Elektroniikkakerho/Led-merkki/kicad/optiem/kuvat/IMG_20201127_135844.jpg

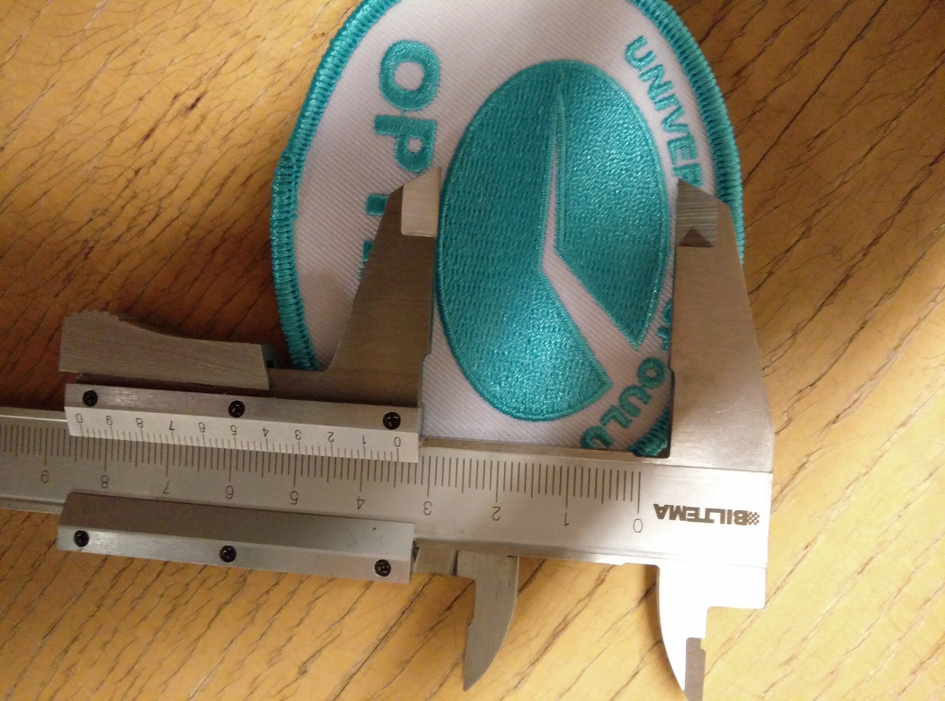
kicad/optiem/kuvat/IMG_20201127_135844.jpg
