Elektroniikkakerho/Led-merkki/kicad/optiem/kuvat/IMG_20201127_140003.jpg

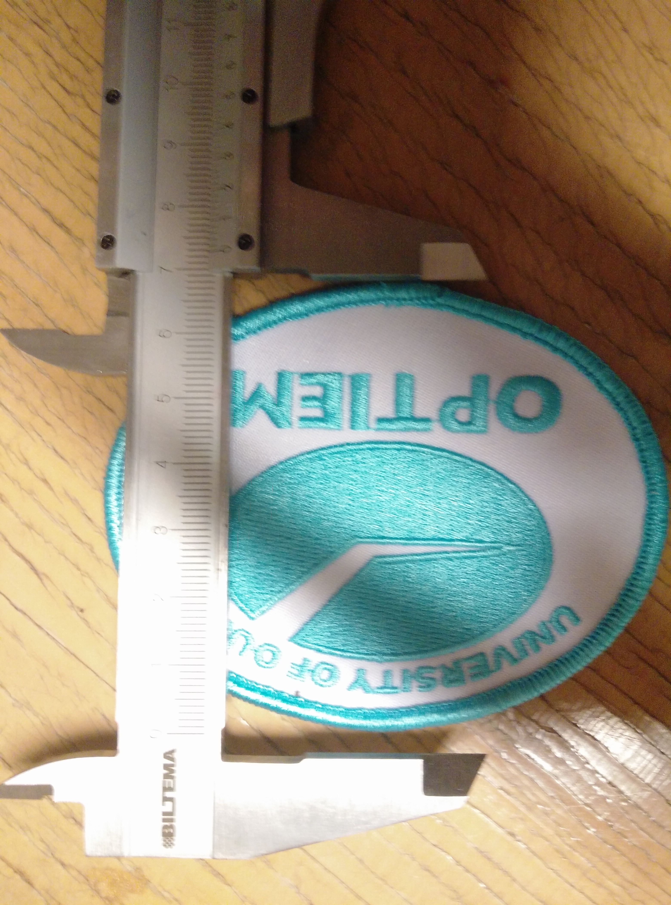
kicad/optiem/kuvat/IMG_20201127_140003.jpg
