Elektroniikkakerho/Led-merkki/kicad/optiem/kuvat/IMG_20201127_140038.jpg

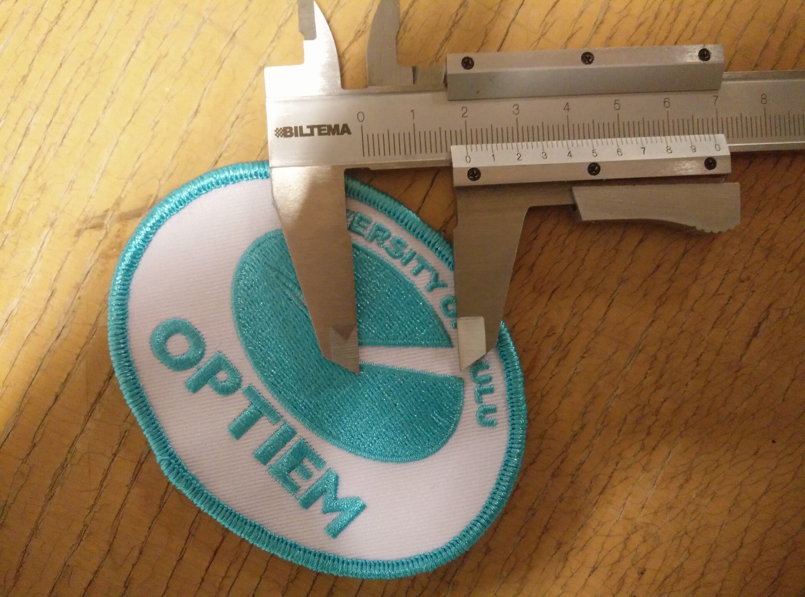
kicad/optiem/kuvat/IMG_20201127_140038.jpg
